NeilTheSeal/tesla_speakers/assets/images/perspective_render_with_speakers.png

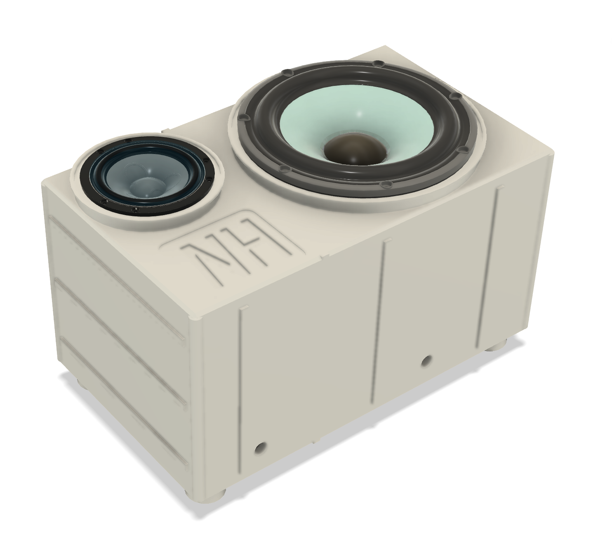
assets/images/perspective_render_with_speakers.png
